area3001/knixx/sw/knis4a/usb.h

#ifndef USB_H_
#define USB_H_

#define USB_INT_MAX_PACKET_SIZE		16
#define USB_BULK_MAX_PACKET_SIZE 	64

#define EP_DATA_OUT(x)	(x + 1)
#define EP_DATA_IN(x)	((x + 1) | 0x80)
#define EP_COMM(x)		((x + 2) | 0x80)

enum usb_itf {
	USB_ITF_CONSOLE	= 0,
	USB_ITF_LOG = 2,
	USB_ITF_TPUART = 4,
	USB_ITF_DFU = 6
};

void usb_setup(void);
void usb_print_console(const char *str);
void usb_print_log(const char *str);
void usb_print_tpuart(const char *str);

#endif
